nobody0know/esp32c3-assistant/c3-assistant/main/sleep_wakeup/sleep_wakeup.c

#include <stdio.h>
#include <string.h>
#include <stdlib.h>
#include <time.h>
#include <sys/time.h>
#include "esp_log.h"
#include "esp_timer.h"
#include "esp_check.h"
#include "driver/uart.h"
#include "esp_sleep.h"
#include "freertos/FreeRTOS.h"
#include "freertos/task.h"
#include "driver/gpio.h"

#define TIMER_WAKEUP_TIME_US    (1 * 100 * 1000)

static const char *TAG = "sleep_wakeup";

esp_err_t register_timer_wakeup(void)
{
    ESP_RETURN_ON_ERROR(esp_sleep_enable_timer_wakeup(TIMER_WAKEUP_TIME_US), TAG, "Configure timer as wakeup source failed");
    ESP_LOGI(TAG, "timer wakeup source is ready");
    return ESP_OK;
}

/* Use boot button as gpio input */
#define GPIO_WAKEUP_NUM         GPIO_NUM_2
/* "Boot" button is active low */
#define GPIO_WAKEUP_LEVEL       0

void wait_gpio_inactive(void)
{
    printf("Waiting for GPIO%d to go high...\n", GPIO_WAKEUP_NUM);
    while (gpio_get_level(GPIO_WAKEUP_NUM) == GPIO_WAKEUP_LEVEL) {
        vTaskDelay(pdMS_TO_TICKS(10));
    }
}

esp_err_t register_gpio_wakeup(void)
{
    // /* Initialize GPIO */
    // gpio_config_t config = {
    //         .pin_bit_mask = BIT64(GPIO_WAKEUP_NUM),
    //         .mode = GPIO_MODE_INPUT,
    //         .pull_down_en = false,
    //         .pull_up_en = false,
    //         .intr_type = GPIO_INTR_DISABLE
    // };
    // ESP_RETURN_ON_ERROR(gpio_config(&config), TAG, "Initialize GPIO%d failed", GPIO_WAKEUP_NUM);

    /* Enable wake up from GPIO */
    ESP_RETURN_ON_ERROR(gpio_wakeup_enable(GPIO_WAKEUP_NUM, GPIO_WAKEUP_LEVEL == 0 ? GPIO_INTR_LOW_LEVEL : GPIO_INTR_HIGH_LEVEL),
                        TAG, "Enable gpio wakeup failed");
    ESP_RETURN_ON_ERROR(esp_sleep_enable_gpio_wakeup(), TAG, "Configure gpio as wakeup source failed");

    /* Make sure the GPIO is inactive and it won't trigger wakeup immediately */
    wait_gpio_inactive();
    ESP_LOGI(TAG, "gpio wakeup source is ready");

    return ESP_OK;
}

static void light_sleep_task(void *args)
{
    while (true) {
        printf("Entering light sleep\n");
        /* To make sure the complete line is printed before entering sleep mode,
         * need to wait until UART TX FIFO is empty:
         */
        uart_wait_tx_idle_polling(CONFIG_ESP_CONSOLE_UART_NUM);

        /* Get timestamp before entering sleep */
        int64_t t_before_us = esp_timer_get_time();

        /* Enter sleep mode */
        esp_light_sleep_start();

        /* Get timestamp after waking up from sleep */
        int64_t t_after_us = esp_timer_get_time();

        /* Determine wake up reason */
        const char* wakeup_reason;
        switch (esp_sleep_get_wakeup_cause()) {
            case ESP_SLEEP_WAKEUP_TIMER:
                wakeup_reason = "timer";
                break;
            case ESP_SLEEP_WAKEUP_GPIO:
                wakeup_reason = "pin";
                break;
                /* Hang-up for a while to switch and execute the uart task
                 * Otherwise the chip may fall sleep again before running uart task */
                vTaskDelay(1);
                break;

            default:
                wakeup_reason = "other";
                break;
        }
        printf("Returned from light sleep, reason: %s, t=%lld ms, slept for %lld ms\n",
                wakeup_reason, t_after_us / 1000, (t_after_us - t_before_us) / 1000);
        if (esp_sleep_get_wakeup_cause() == ESP_SLEEP_WAKEUP_GPIO) {
            /* Waiting for the gpio inactive, or the chip will continuously trigger wakeup*/
            wait_gpio_inactive();
        }
    }
    vTaskDelete(NULL);
}

void sleep_wakeup_init(void)
{
    /* Enable wakeup from light sleep by gpio */
    register_gpio_wakeup();
    /* Enable wakeup from light sleep by timer */
    register_timer_wakeup();

    xTaskCreate(light_sleep_task, "light_sleep_task", 4096, NULL, 6, NULL);
}
