nobody0know/esp32c3-assistant/c3-assistant/main/epaper/EPD_Font.h

#ifndef _EPD_FONT_H_
#define _EPD_FONT_H_


//图片取模配置使用软件 PCtoLCD2002
//点阵格式:阴码
//取模走向:逆向(低位在前)
//取模方式:
//				 字符:列行式 C51格式 
//				 中文:逐行式 C51格式
//字符尺寸限制:字符宽度限制为8的倍数


const unsigned char asc2_0806[][6] =
{
{0x00, 0x00, 0x00, 0x00, 0x00, 0x00},// sp
{0x00, 0x00, 0x00, 0x2f, 0x00, 0x00},// !
{0x00, 0x00, 0x07, 0x00, 0x07, 0x00},// "
{0x00, 0x14, 0x7f, 0x14, 0x7f, 0x14},// #
{0x00, 0x24, 0x2a, 0x7f, 0x2a, 0x12},// $
{0x00, 0x62, 0x64, 0x08, 0x13, 0x23},// %
{0x00, 0x36, 0x49, 0x55, 0x22, 0x50},// &
{0x00, 0x00, 0x05, 0x03, 0x00, 0x00},// '
{0x00, 0x00, 0x1c, 0x22, 0x41, 0x00},// (
{0x00, 0x00, 0x41, 0x22, 0x1c, 0x00},// )
{0x00, 0x14, 0x08, 0x3E, 0x08, 0x14},// *
{0x00, 0x08, 0x08, 0x3E, 0x08, 0x08},// +
{0x00, 0x00, 0x00, 0xA0, 0x60, 0x00},// ,
{0x00, 0x08, 0x08, 0x08, 0x08, 0x08},// -
{0x00, 0x00, 0x60, 0x60, 0x00, 0x00},// .
{0x00, 0x20, 0x10, 0x08, 0x04, 0x02},// /
{0x00, 0x3E, 0x51, 0x49, 0x45, 0x3E},// 0
{0x00, 0x00, 0x42, 0x7F, 0x40, 0x00},// 1
{0x00, 0x42, 0x61, 0x51, 0x49, 0x46},// 2
{0x00, 0x21, 0x41, 0x45, 0x4B, 0x31},// 3
{0x00, 0x18, 0x14, 0x12, 0x7F, 0x10},// 4
{0x00, 0x27, 0x45, 0x45, 0x45, 0x39},// 5
{0x00, 0x3C, 0x4A, 0x49, 0x49, 0x30},// 6
{0x00, 0x01, 0x71, 0x09, 0x05, 0x03},// 7
{0x00, 0x36, 0x49, 0x49, 0x49, 0x36},// 8
{0x00, 0x06, 0x49, 0x49, 0x29, 0x1E},// 9
{0x00, 0x00, 0x36, 0x36, 0x00, 0x00},// :
{0x00, 0x00, 0x56, 0x36, 0x00, 0x00},// ;
{0x00, 0x08, 0x14, 0x22, 0x41, 0x00},// <
{0x00, 0x14, 0x14, 0x14, 0x14, 0x14},// =
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



};




typedef struct 
{
	unsigned char Index[2];	
	unsigned char Msk[24];
}typFNT_GB12; 


const typFNT_GB12 tfont12[]=
{

};

typedef struct 
{
	unsigned char Index[2];	
	unsigned char Msk[32];
}typFNT_GB16; 


const typFNT_GB16 tfont16[]={
	
};


typedef struct 
{
	unsigned char Index[2];	
	unsigned char Msk[72];
}typFNT_GB24; 


const typFNT_GB24 tfont24[]={

};


typedef struct 
{
	unsigned char Index[2];	
	unsigned char Msk[128];
}typFNT_GB32; 


const typFNT_GB32 tfont32[]={

};





#endif
