nobody0know/esp32c3-assistant/c3-assistant/main/epaper/Pic.h

#ifndef _PIC_H_
#define _PIC_H_

const unsigned char gImage_1[5624] = { /* 0X01,0X01,0X28,0X01,0X98,0X00, */
0X00,0X00,0X03,0XFF,0XFF,0XFF,0XFF,0XFF,0XFF,0XFF,0XFE,0XFF,0XFF,0XFF,0XFF,0XFF,
0XFF,0XFF,0XFF,0X00,0X00,0X03,0XFF,0XFF,0XFF,0XFF,0XFF,0XFF,0XFF,0XFE,0XFF,0XFF,
0XFF,0XFF,0XFF,0XFF,0XFF,0XFF,0X00,0X00,0X03,0XFF,0XFF,0XFF,0XFF,0XFF,0XFF,0XFF,
0XFE,0XFF,0XFF,0XFF,0XFF,0XFF,0XFF,0XFF,0XFF,0X01,0X80,0XC3,0XFF,0XFF,0XFF,0XFF,
0XFF,0XFF,0XFF,0XFE,0XFF,0XFF,0XFF,0XFF,0XFF,0XFF,0XFF,0XFF,0X02,0X01,0X43,0XFF,
0XFF,0XFF,0XFF,0XFF,0XFF,0XFF,0XFE,0XFF,0XFF,0XFF,0XFF,0XFF,0XFF,0XFF,0XFF,0X04,
0X02,0X43,0XFF,0XFF,0XFF,0XFF,0XFF,0XFF,0XFF,0XFE,0XFE,0X7F,0XFF,0XFF,0XFF,0XFF,
0XFF,0XFF,0X04,0X04,0X43,0XFF,0XFF,0XFF,0XFF,0XFF,0XFF,0XFF,0XFE,0XFE,0XFF,0XFF,
0XFF,0XFF,0XFF,0XFF,0XFF,0X04,0X08,0X43,0XFF,0XFF,0XFF,0XFF,0XFF,0XFF,0XFF,0XFE,
0XFE,0XFE,0XFF,0XFF,0XFF,0XFF,0XFF,0XFF,0X04,0X10,0X43,0XFF,0XFF,0XFF,0XFF,0XFF,
0XFF,0XFF,0XFE,0XFE,0X00,0XFF,0XFF,0XFF,0XFF,0XFF,0XFF,0X02,0X20,0X43,0XFF,0XFF,
0XFF,0XFF,0XFF,0XFF,0XFF,0XFE,0XFE,0XFE,0XFF,0XFF,0XFF,0XFF,0XFF,0XFF,0X01,0XC1,
0XC3,0XFF,0XFF,0XFF,0XFF,0XFF,0XFF,0XFF,0XFE,0XFE,0XFF,0XFF,0XFF,0XFF,0XFF,0XFF,
0XFF,0X00,0X00,0X03,0XFF,0XFF,0XFF,0XFF,0XFF,0XFF,0XFF,0XFE,0XFE,0X7F,0XFF,0XFF,
0XFF,0XFF,0XFF,0XFF,0X00,0X00,0X03,0XFF,0XFF,0XFF,0XFF,0XFF,0XFF,0XFF,0XFE,0XFF,
0X83,0XFF,0XFF,0XFF,0XFF,0XFF,0XFF,0X00,0XFE,0X03,0XFF,0XFF,0XFF,0XFF,0XFF,0XFF,
0XFF,0XFE,0XFF,0X7D,0XFF,0XFF,0XFF,0XFF,0XFF,0XFF,0X03,0X01,0X83,0XFF,0XFF,0XFF,
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
0XFF,0XFF,0XFF,0XFF,0XFF,0XFF,0XFF,0XFF,0XFF,0XFF,0XFF,0XFF,0XFF,0XFF,0XFF,0XFF,
0XFF,0XFF,0XFF,0XFF,0XFF,0XFF,0XFF,0XFF,0XFF,0XFF,0XFF,0XFF,0XFF,0XFF,0XFF,0XFF,
0XFF,0XFF,0XFF,0XFF,0XFF,0XFF,0XFF,0XFF,0XFF,0XFF,0XFF,0XFF,0XFF,0XFF,0XFF,0XFF,
0XFF,0XFF,0XFF,0XFF,0XFF,0XFF,0XFF,0XFF,0XFF,0XFF,0XFF,0XFF,0XFF,0XFF,0XFF,0XFF,
0XFF,0XFF,0XFF,0XFF,0XFF,0XFF,0XFF,0XFF,0XFF,0XFF,0XFF,0XFF,0XFF,0XFF,0XFF,0XFF,
0XFF,0XFF,0XFF,0XFF,0XFF,0XFF,0XFF,0XFF,0XFF,0XFF,0XFF,0XFF,0XFF,0XFF,0XFF,0XFF,
0XFF,0XFF,0XFF,0XFF,0XFF,0XFF,0XFF,0XFF,0XFF,0XFF,0XFF,0XFF,0XFF,0XFF,0XFF,0XFF,
0XFF,0XFF,0XFF,0XFF,0XFF,0XFF,0XFF,0XFF,0XFF,0XFF,0XFF,0XFF,0XFF,0XFF,0XFF,0XFF,
0XFF,0XFF,0XFF,0XFF,0XFF,0XFF,0XFF,0XFF,0XFF,0XFF,0XFF,0XFF,0XFF,0XFF,0XFF,0XFF,
0XFF,0XFF,0XFF,0XFF,0XFF,0XFF,0XFF,0XFF,0XFF,0XFF,0XFF,0XFF,0XFF,0XFF,0XFF,0XFF,
0XFF,0XFF,0XFF,0XFF,0XFF,0XFF,0XFF,0XFF,0XFF,0XFF,0XFF,0XFF,0XFF,0XFF,0XFF,0XFF,
0XFF,0XFF,0XFF,0XFF,0XFF,0XFF,0XFF,0XFF,0XFF,0XFF,0XFF,0XFF,0XFF,0XFF,0XFF,0XFF,
};

#endif
