nobody0know/esp32c3-assistant/c3-assistant/main/epaper/EPD_GUI.h

#ifndef _EPD_GUI_H_
#define _EPD_GUI_H_

#include "EPD.h"

typedef struct {
	uint8_t *Image;
	uint16_t width;
	uint16_t height;
	uint16_t widthMemory;
	uint16_t heightMemory;
	uint16_t color;
	uint16_t rotate;
	uint16_t widthByte;
	uint16_t heightByte;
	
}PAINT;
extern PAINT Paint;

//定义E-Paper显示方向 
/*******************
Rotaion:0-0度方向
Rotaion:90-90度方向
Rotaion:180-180度方向
Rotaion:270-270度方向
*******************/
#define Rotation 0  


void Paint_NewImage(uint8_t *image,uint16_t Width,uint16_t Height,uint16_t Rotate,uint16_t Color); 					 //创建画布控制显示方向
void Paint_SetPixel(uint16_t Xpoint,uint16_t Ypoint,uint16_t Color);
void Paint_Clear(uint8_t Color);
void EPD_DrawLine(uint16_t Xstart,uint16_t Ystart,uint16_t Xend,uint16_t Yend,uint16_t Color);
void EPD_DrawRectangle(uint16_t Xstart,uint16_t Ystart,uint16_t Xend,uint16_t Yend,uint16_t Color,uint8_t mode);  //画矩形
void EPD_DrawCircle(uint16_t X_Center,uint16_t Y_Center,uint16_t Radius,uint16_t Color,uint8_t mode);        //画圆
void EPD_ShowChar(uint16_t x,uint16_t y,uint16_t chr,uint16_t size1,uint16_t color);                         //显示字符
void EPD_ShowString(uint16_t x,uint16_t y,uint8_t *chr,uint16_t size1,uint16_t color);                       //显示字符串
void EPD_ShowNum(uint16_t x,uint16_t y,uint32_t num,uint16_t len,uint16_t size1,uint16_t color);                  //显示数字
void EPD_ShowPicture(uint16_t x,uint16_t y,uint16_t sizex,uint16_t sizey,const uint8_t BMP[],uint16_t Color);			//显示图片      
void EPD_ClearWindows(uint16_t xs,uint16_t ys,uint16_t xe,uint16_t ye,uint16_t color);
void EPD_ShowFloatNum1(uint16_t x,uint16_t y,float num,uint8_t len,uint8_t pre,uint8_t sizey,uint8_t color);
void EPD_ShowWatch(uint16_t x,uint16_t y,float num,uint8_t len,uint8_t pre,uint8_t sizey,uint8_t color);

void EPD_ShowChinese(uint16_t x,uint16_t y,uint8_t *s,uint8_t sizey,uint16_t color);//显示汉字串
void EPD_ShowChinese12x12(uint16_t x,uint16_t y,uint8_t *s,uint8_t sizey,uint16_t color);//显示单个12x12汉字
void EPD_ShowChinese16x16(uint16_t x,uint16_t y,uint8_t *s,uint8_t sizey,uint16_t color);//显示单个16x16汉字
void EPD_ShowChinese24x24(uint16_t x,uint16_t y,uint8_t *s,uint8_t sizey,uint16_t color);//显示单个24x24汉字
void EPD_ShowChinese32x32(uint16_t x,uint16_t y,uint8_t *s,uint8_t sizey,uint16_t color);//显示单个32x32汉字

#endif
